Andreasgdp/Robot-hand-semester-2/Cpp Rasbarry PI/RobotHand/gripper.h

#ifndef GRIPPER_H
#define GRIPPER_H
#include <string>


class Gripper
{
public:
    Gripper();
    ~Gripper();
    void grip(std::string width, std::string speed, std::string force);
    void release(std::string width, std::string speed);
    void setWidth(int width);
    int getWidth();
    int getRun();
    static void setRun(int value);
    static int getSpeed();
    static void setSpeed(int speed);



private:
    static int _width, _speed, _force;
    static int _run;
    int scale = 1000;
};

#endif // GRIPPER_H
